cwahlmann/vz200/3d-model/aufkleber_tasten_einzeln/key_1.png

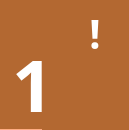
3d-model/aufkleber_tasten_einzeln/key_1.png
