cwahlmann/vz200/3d-model/aufkleber_tasten_einzeln/key_5.png

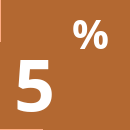
3d-model/aufkleber_tasten_einzeln/key_5.png
