cwahlmann/vz200/3d-model/aufkleber_tasten_einzeln/key_8.png

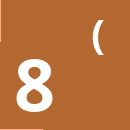
3d-model/aufkleber_tasten_einzeln/key_8.png
