cwahlmann/vz200/3d-model/aufkleber_tasten_einzeln/key_I.png

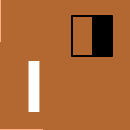
3d-model/aufkleber_tasten_einzeln/key_I.png
