cwahlmann/vz200/3d-model/aufkleber_tasten_einzeln/key_M.png

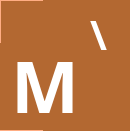
3d-model/aufkleber_tasten_einzeln/key_M.png
