cwahlmann/vz200/3d-model/aufkleber_tasten_einzeln/key_minus.png

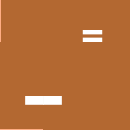
3d-model/aufkleber_tasten_einzeln/key_minus.png
