cwahlmann/vz200/3d-model/aufkleber_tasten_einzeln/key_N.png

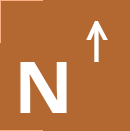
3d-model/aufkleber_tasten_einzeln/key_N.png
