cwahlmann/vz200/3d-model/aufkleber_tasten_einzeln/key_Q.png

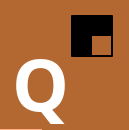
3d-model/aufkleber_tasten_einzeln/key_Q.png
