cwahlmann/vz200/3d-model/Lüftungsgitter.png

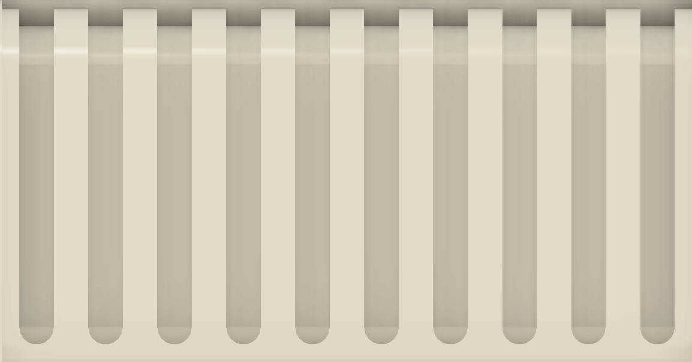
3d-model/Lüftungsgitter.png
