cwahlmann/vz200/3d-model/Lüftungsgitter_transparent.png

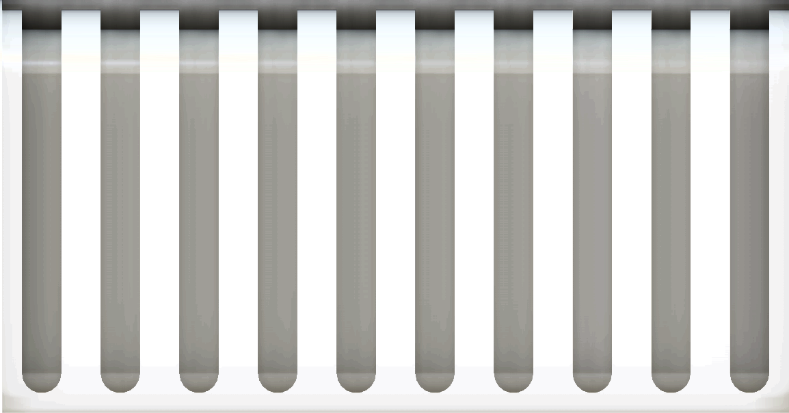
3d-model/Lüftungsgitter_transparent.png
