cwahlmann/vz200/3d-model/Rückseite Aufkleber.png

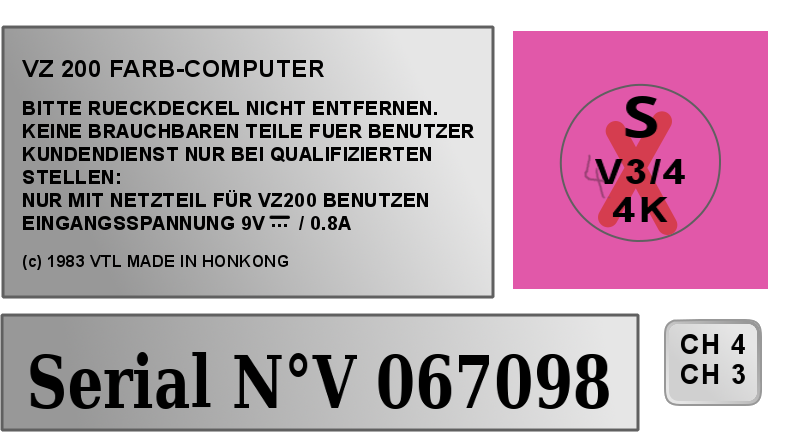
3d-model/Rückseite Aufkleber.png
