cwahlmann/vz200/3d-model/Tastatur_Aufkleber.png

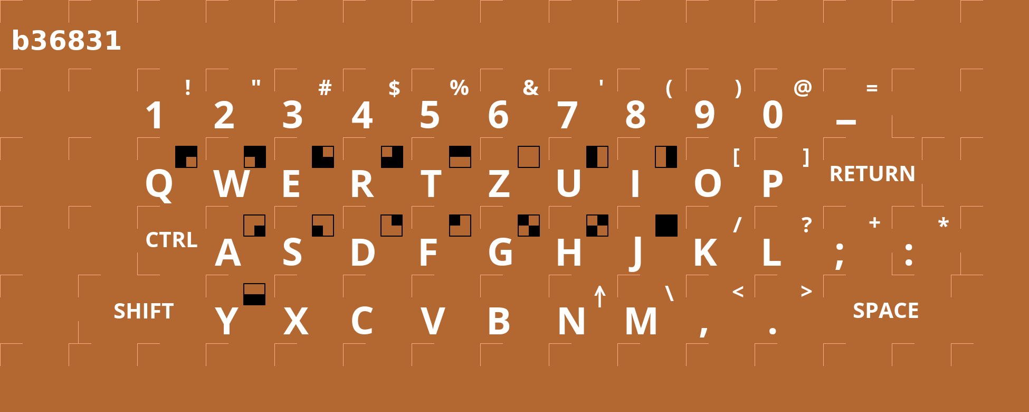
3d-model/Tastatur_Aufkleber.png
