cwahlmann/vz200/3d-model/Tastatur_Aufkleber_7x_70perc_A4.png

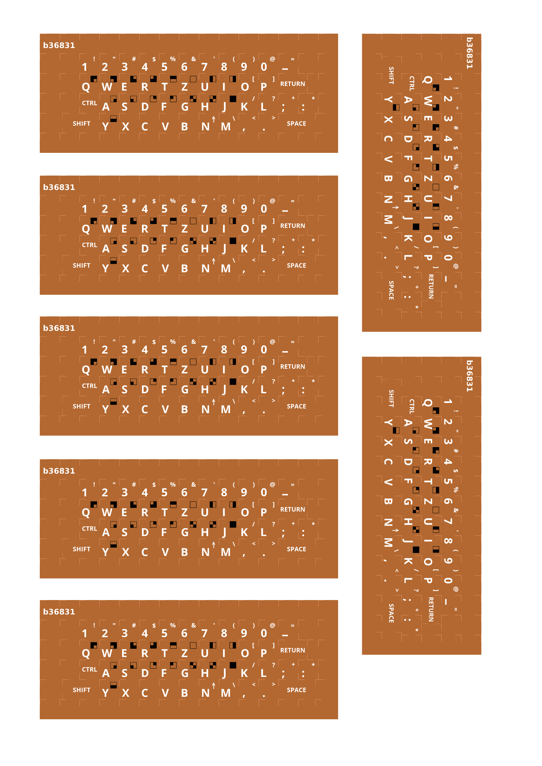
3d-model/Tastatur_Aufkleber_7x_70perc_A4.png
