cwahlmann/vz200/3d-model/Tastatur_mini_A4.png

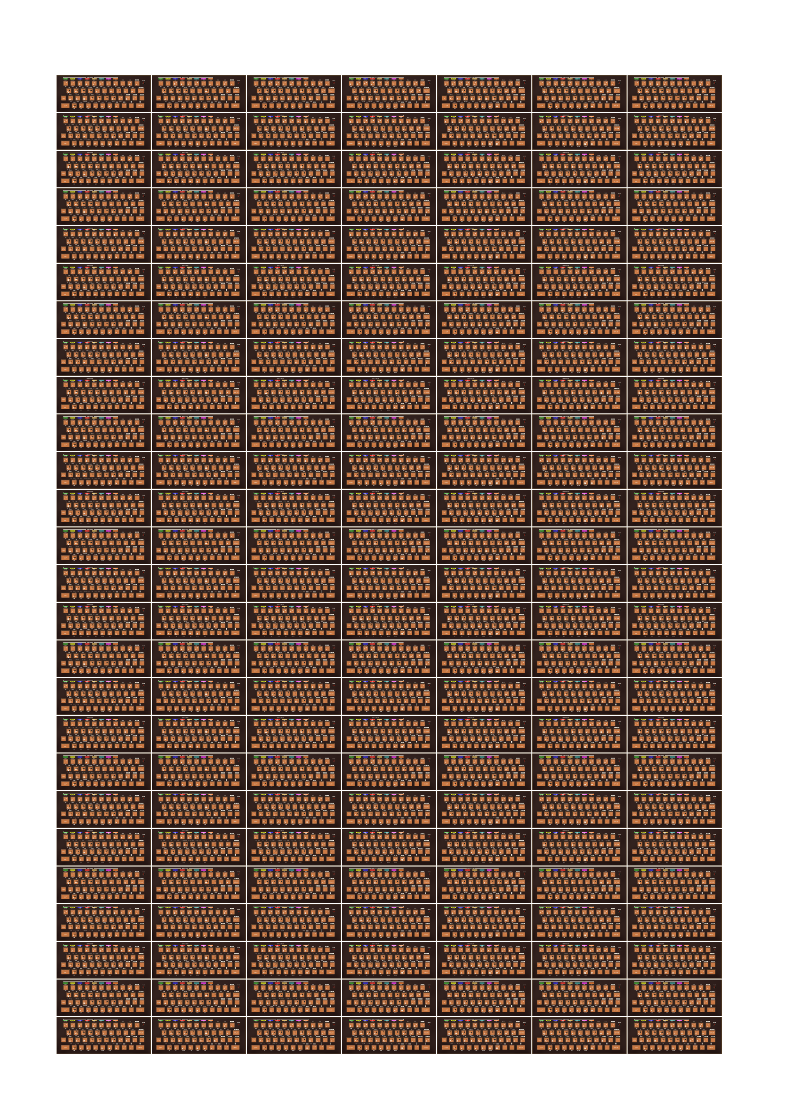
3d-model/Tastatur_mini_A4.png
