cwahlmann/vz200/3d-model/tastaturschabloben_3x70_1x50_A4.png

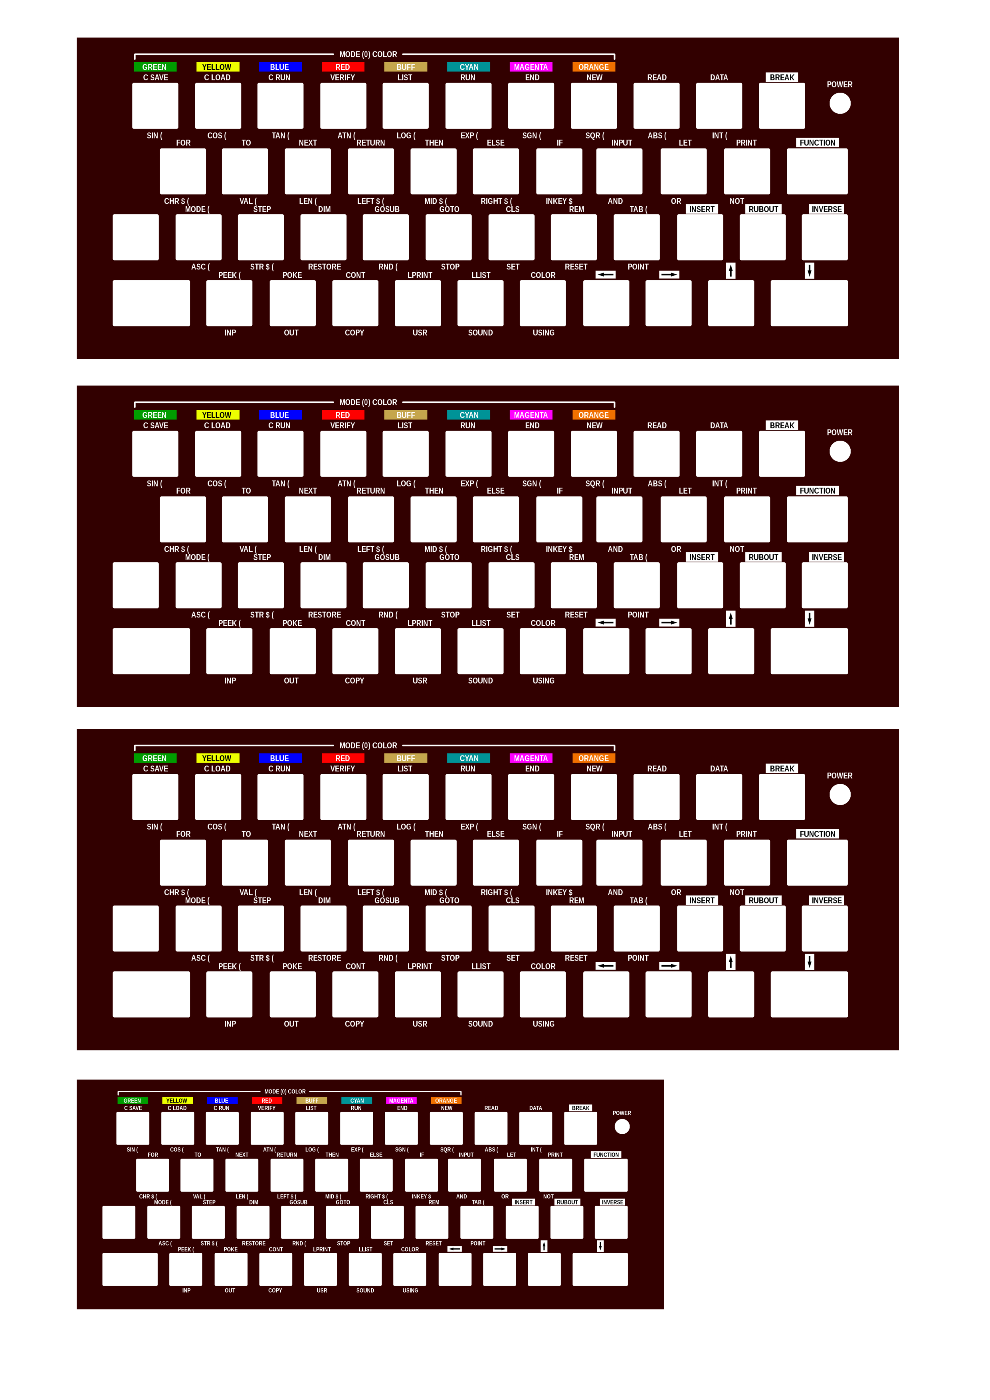
3d-model/tastaturschabloben_3x70_1x50_A4.png
