cwahlmann/vz200/3d-model/Tastaturschablone.png

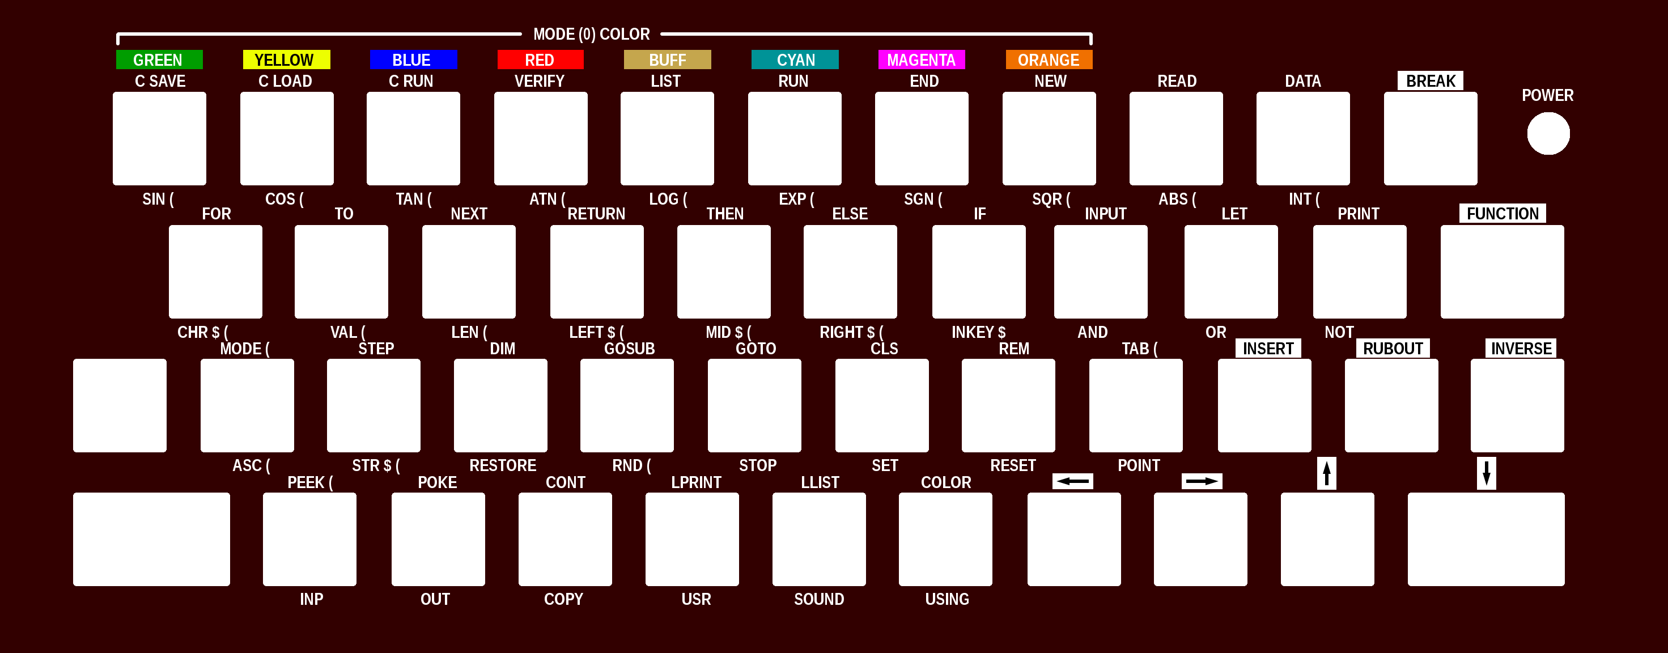
3d-model/Tastaturschablone.png
