cwahlmann/vz200/3d-model/VZ200-background.png

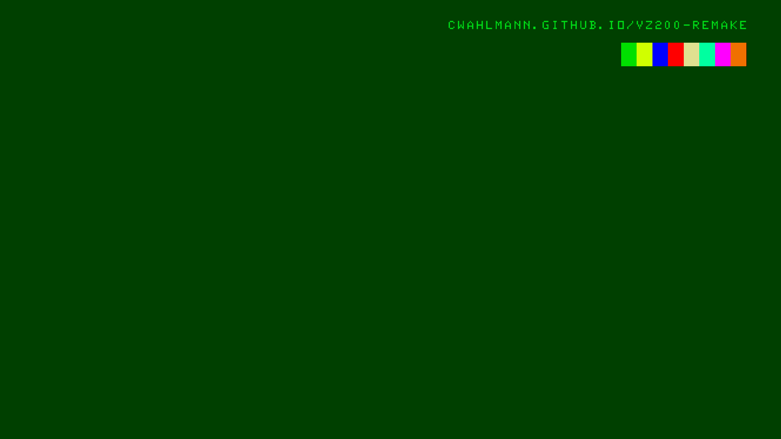
3d-model/VZ200-background.png
