cwahlmann/vz200/3d-model/vz200.png

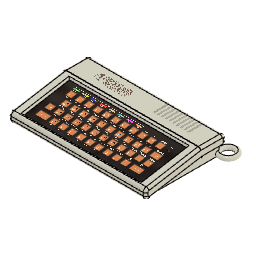
3d-model/vz200.png
