cwahlmann/vz200/emulator/desktop-wallpaper-2.png

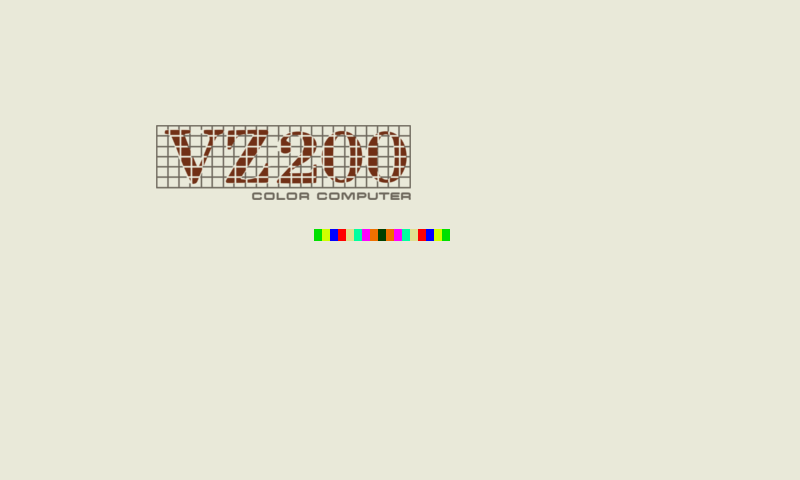
emulator/desktop-wallpaper-2.png
