cwahlmann/vz200/emulator/desktop-wallpaper-3.png

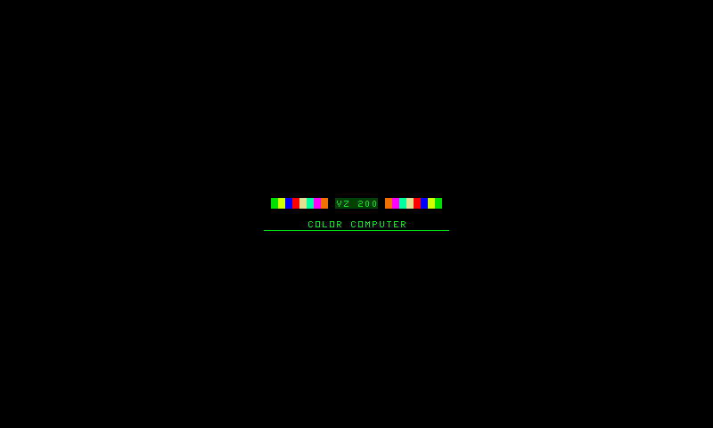
emulator/desktop-wallpaper-3.png
