cwahlmann/vz200/emulator/Tastatur.png

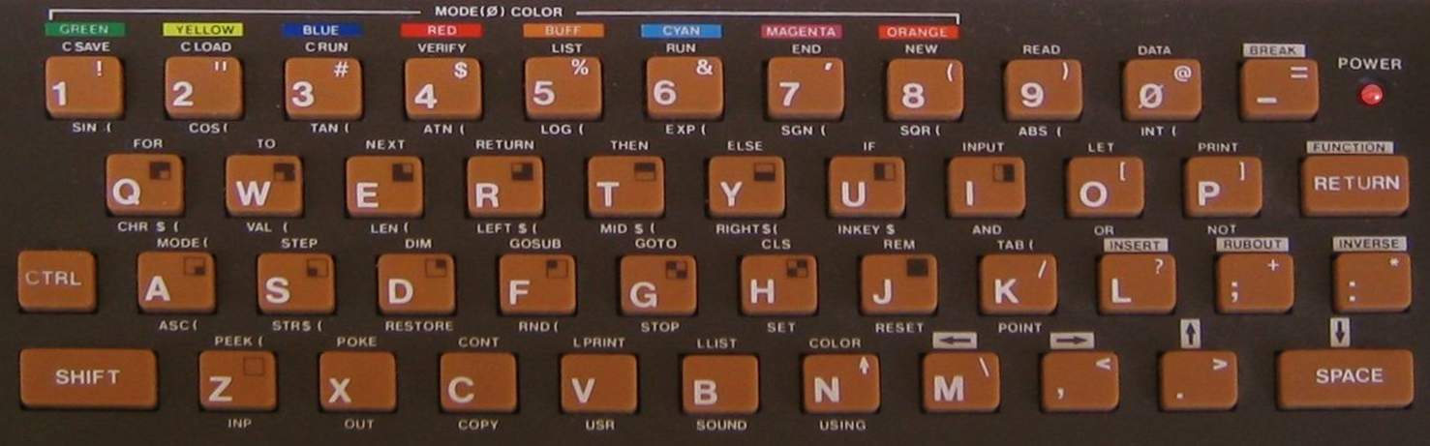
emulator/Tastatur.png
