cwahlmann/vz200/monitor/ASIS-Vintage-1983-RCA-CRT-13-Color-TV-_57 (2).jpg

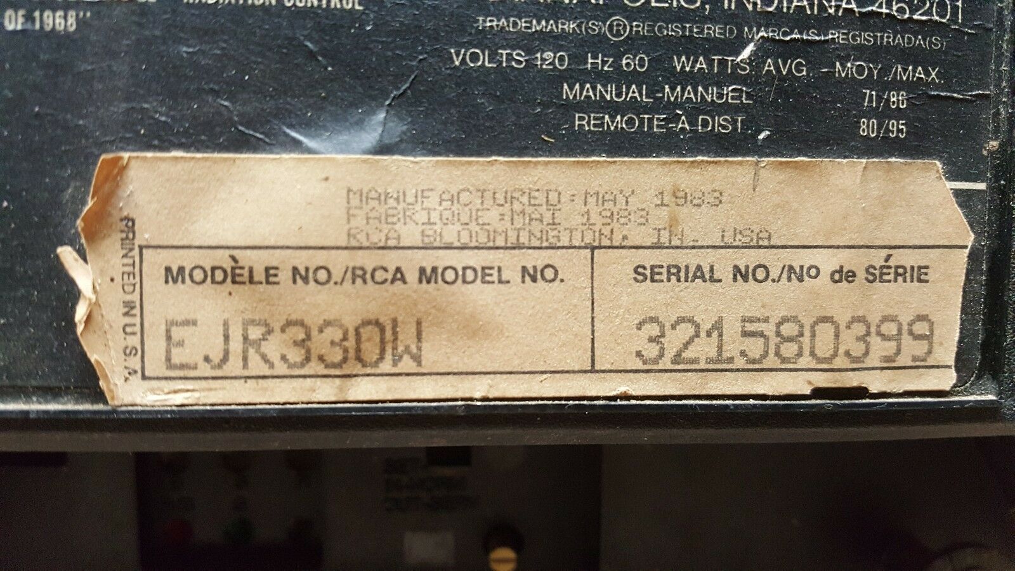
monitor/ASIS-Vintage-1983-RCA-CRT-13-Color-TV-_57 (2).jpg
