cwahlmann/vz200/screenshots/20190511_203651.jpg

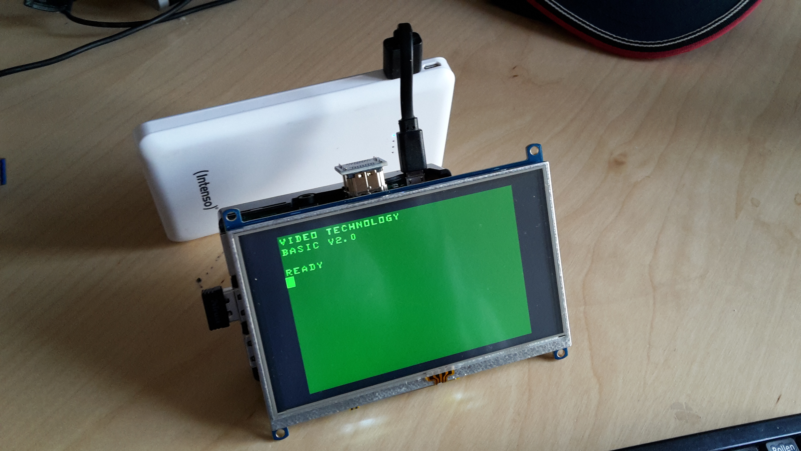
screenshots/20190511_203651.jpg
