cwahlmann/vz200/screenshots/20190511_203712.jpg

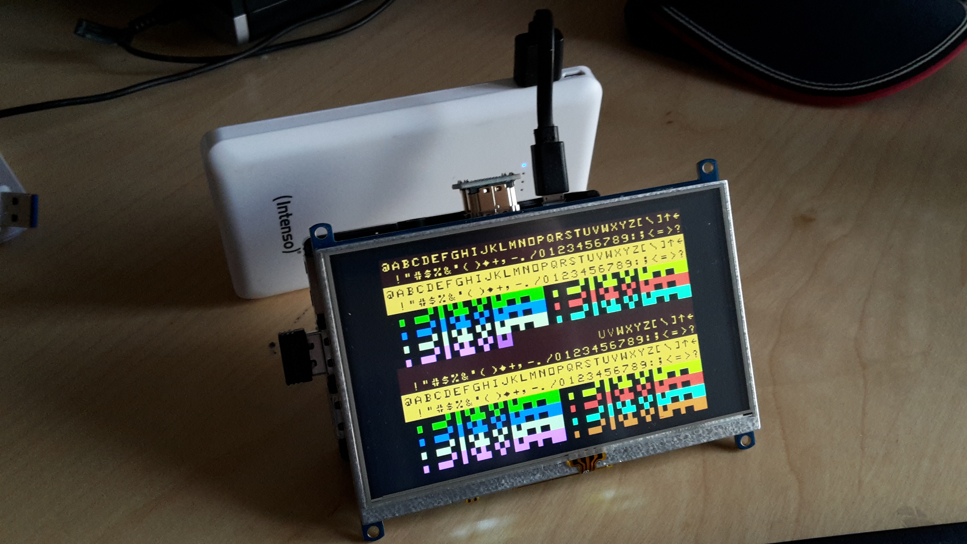
screenshots/20190511_203712.jpg
