cwahlmann/vz200/screenshots/20190511_203717.jpg

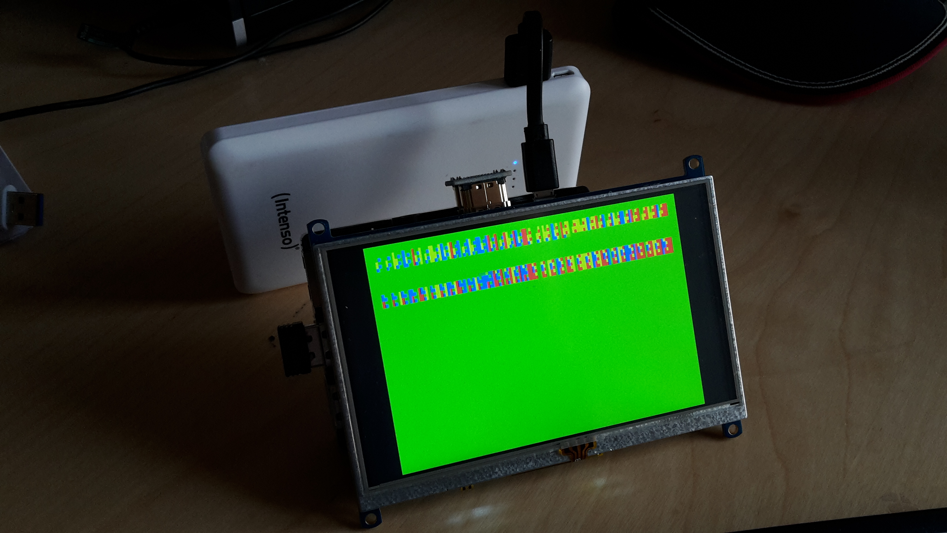
screenshots/20190511_203717.jpg
