cwahlmann/vz200/screenshots/20190511_203816.jpg

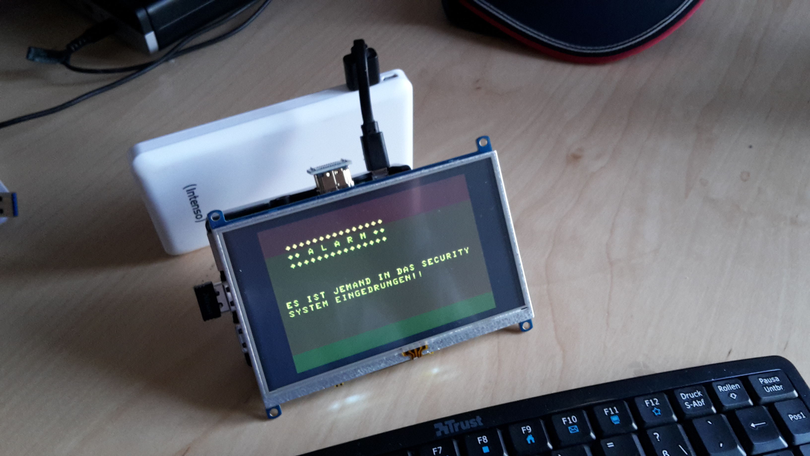
screenshots/20190511_203816.jpg
