cwahlmann/vz200/screenshots/halloWeltAsm.jpg

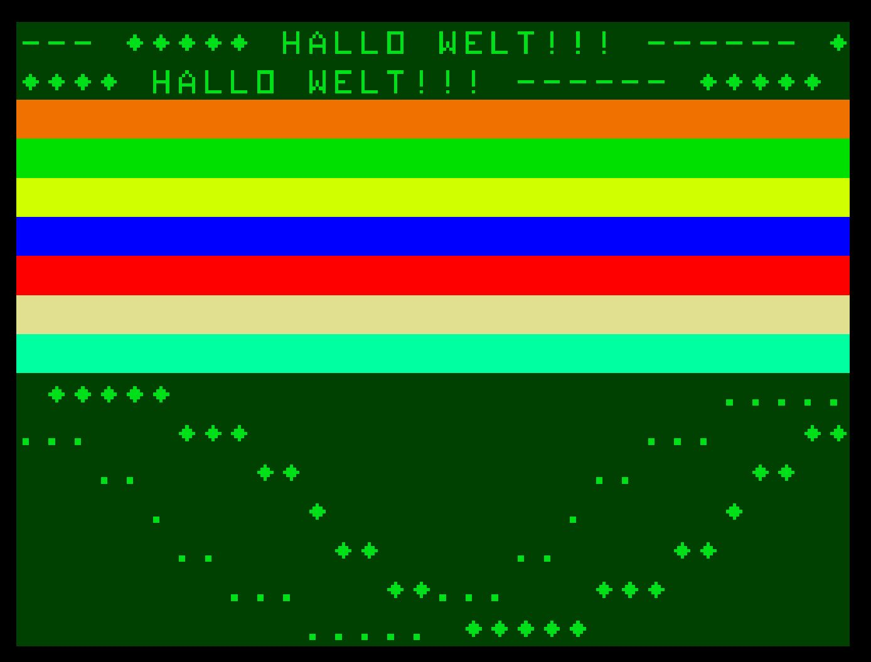
screenshots/halloWeltAsm.jpg
