cwahlmann/vz200/screenshots/Prototyp-02.jpg

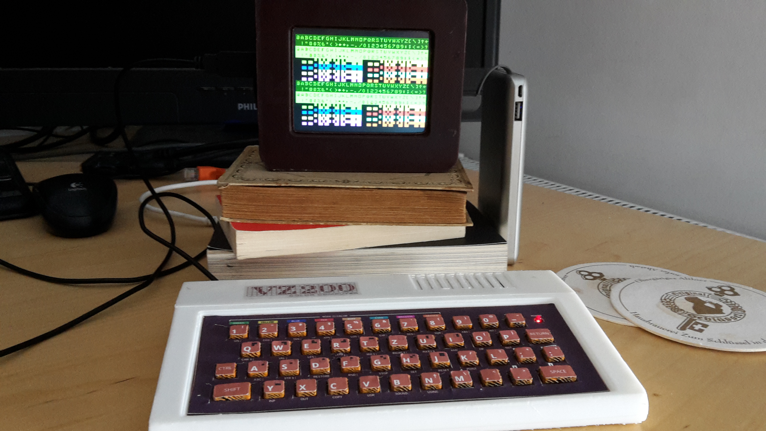
screenshots/Prototyp-02.jpg
