cwahlmann/vz200/screenshots/Prototyp-03.jpg

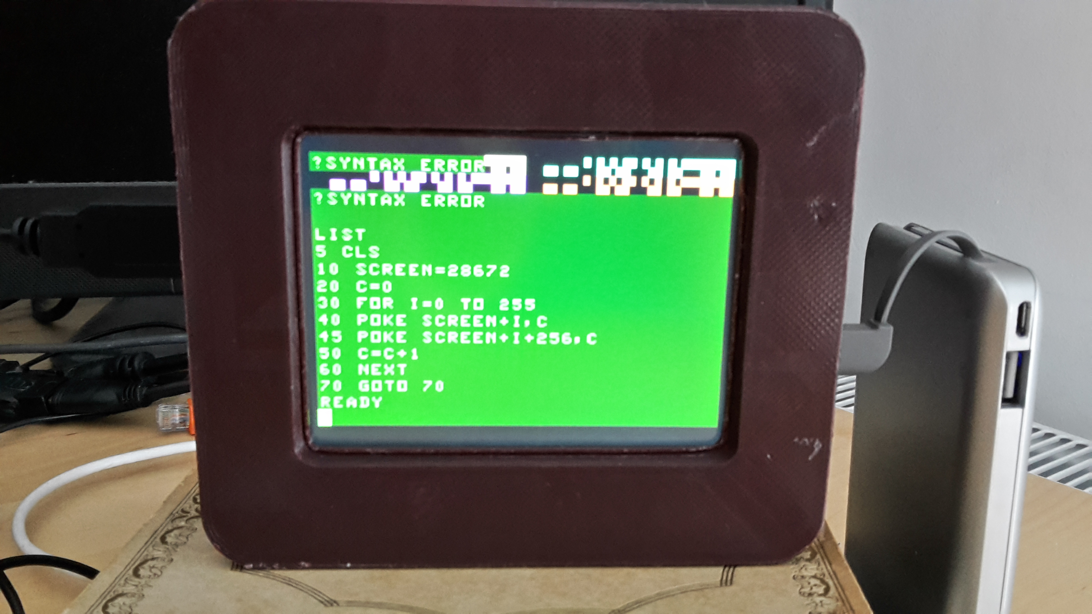
screenshots/Prototyp-03.jpg
