cwahlmann/vz200/screenshots/Prototyp-04.jpg

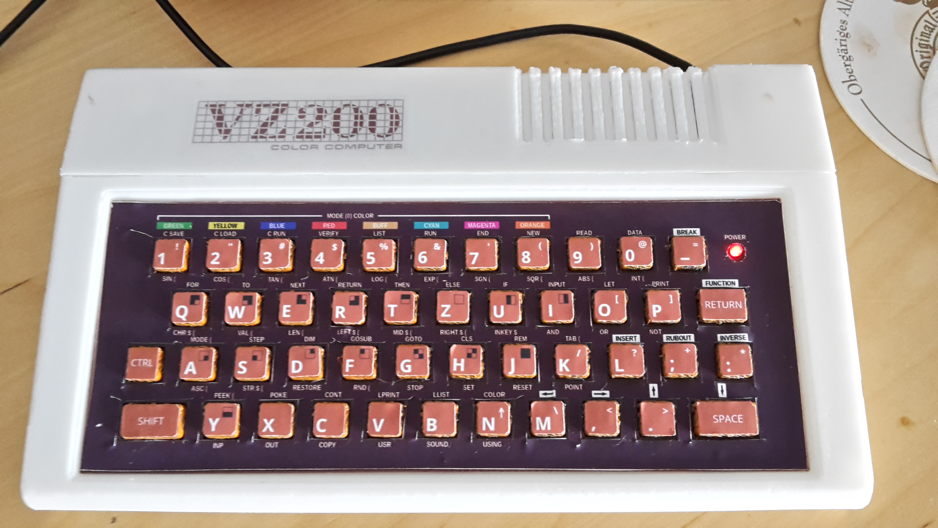
screenshots/Prototyp-04.jpg
