cwahlmann/vz200/screenshots/Prototyp-05.jpg

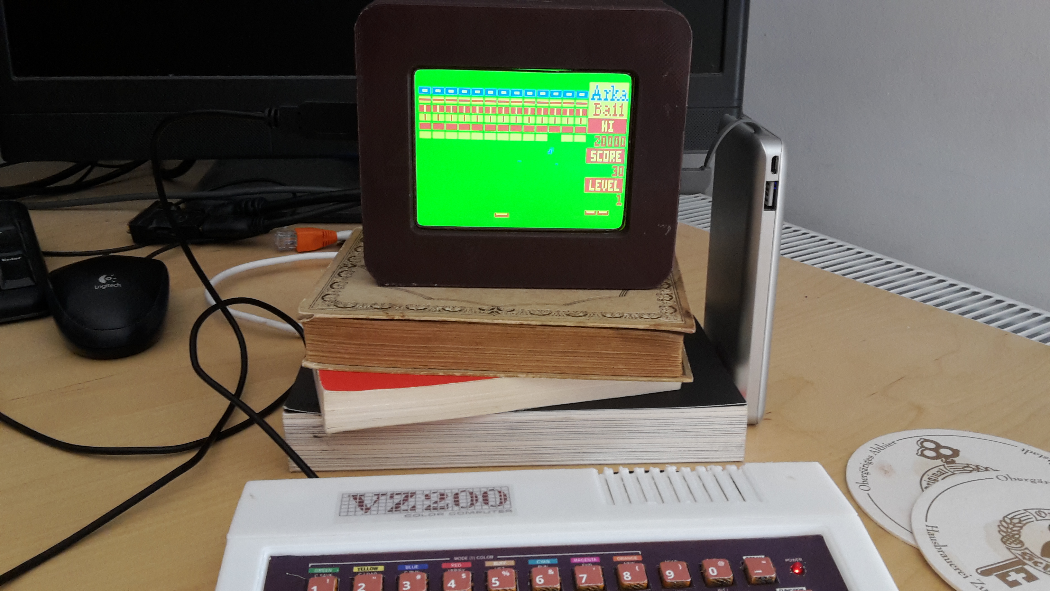
screenshots/Prototyp-05.jpg
