cwahlmann/vz200/screenshots/Prototyp_01.jpg

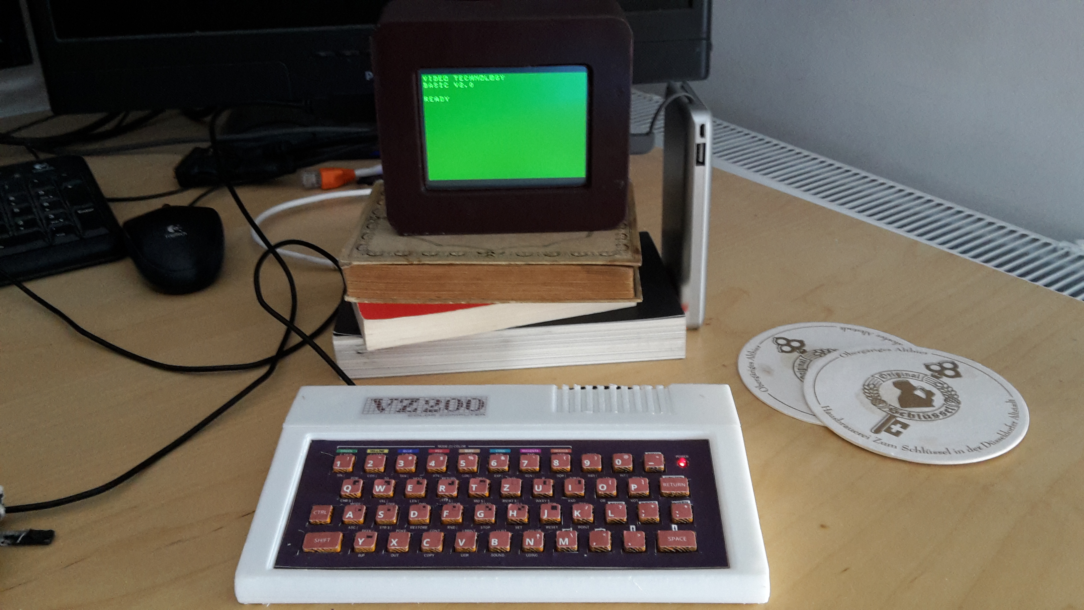
screenshots/Prototyp_01.jpg
