cwahlmann/vz200/screenshots/tastatur_orange_lack_50perc_1.jpg

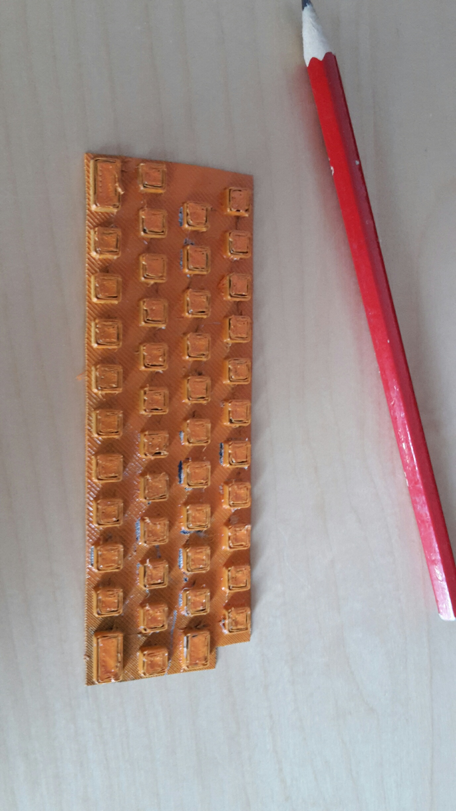
screenshots/tastatur_orange_lack_50perc_1.jpg
