cwahlmann/vz200/screenshots/tastatur_orange_lack_70perc_1.jpg

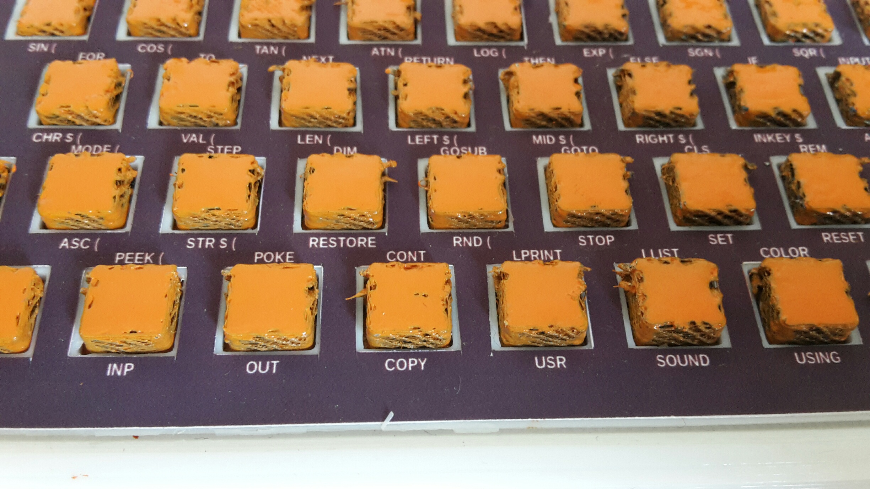
screenshots/tastatur_orange_lack_70perc_1.jpg
