cwahlmann/vz200/screenshots/tastatur_orange_lack_70perc_2.jpg

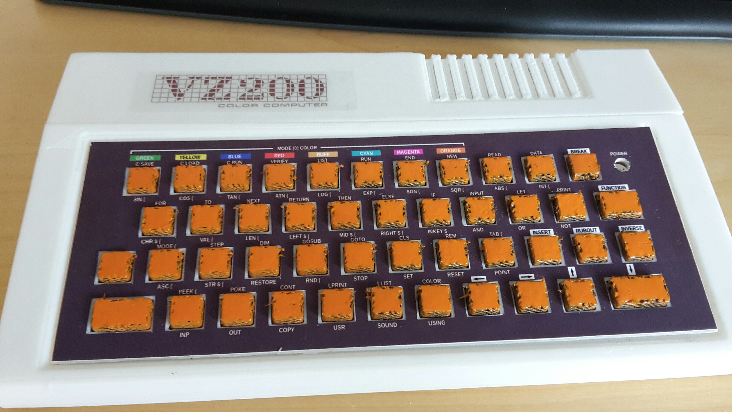
screenshots/tastatur_orange_lack_70perc_2.jpg
