cwahlmann/vz200/screenshots/tastaturfolie_angepasst_1.jpg

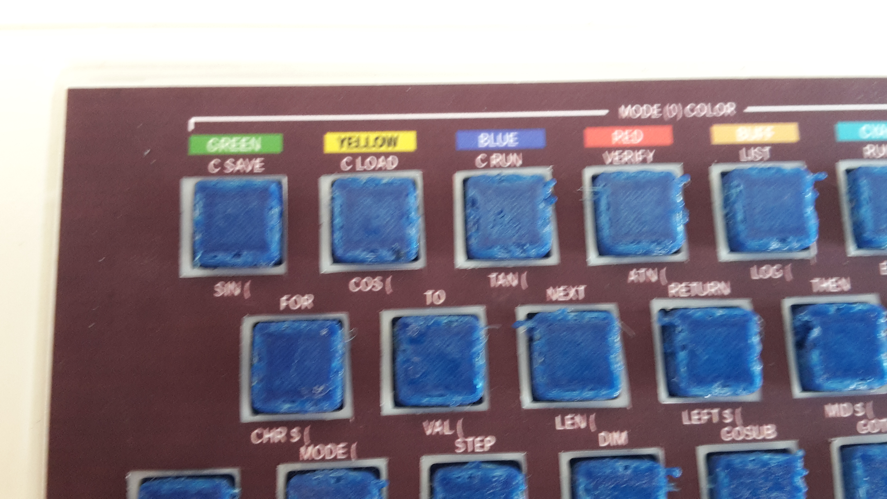
screenshots/tastaturfolie_angepasst_1.jpg
