cwahlmann/vz200/screenshots/tastaturfolie_angepasst_2.jpg

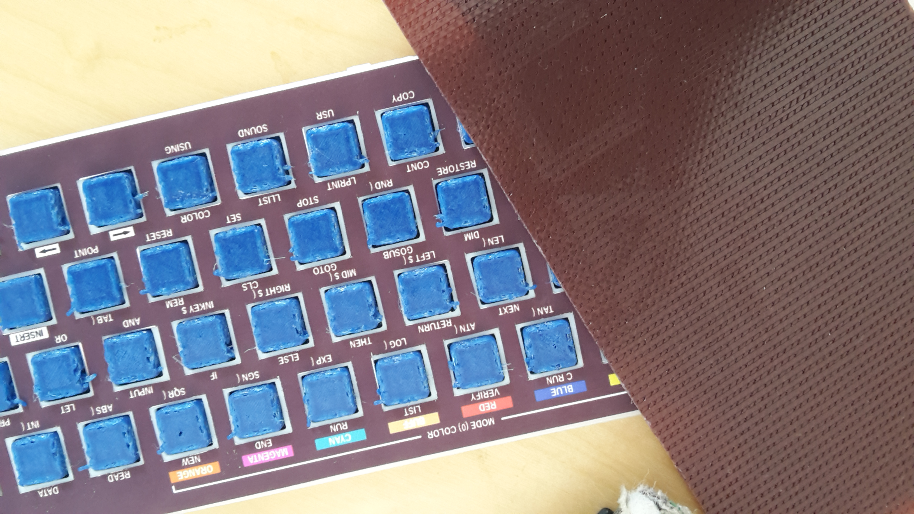
screenshots/tastaturfolie_angepasst_2.jpg
