cwahlmann/vz200/screenshots/tastaturfolie_angepasst_3.jpg

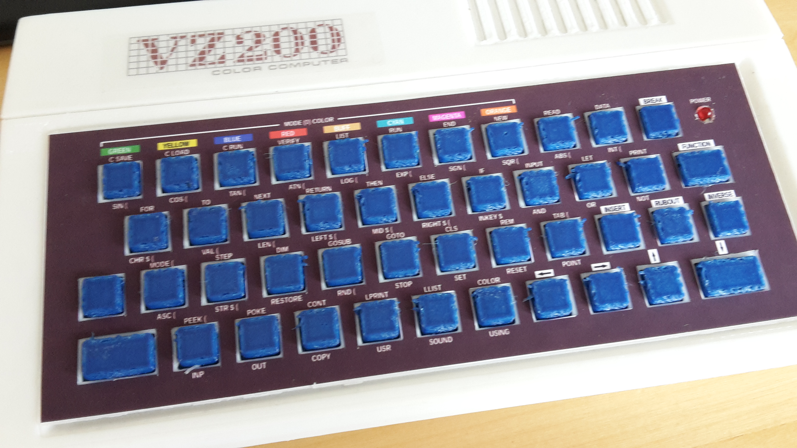
screenshots/tastaturfolie_angepasst_3.jpg
