cwahlmann/vz200/3d-model/drucke/stl/VZ200_Gehäuse unten_rechteSeite_test_70%.stl

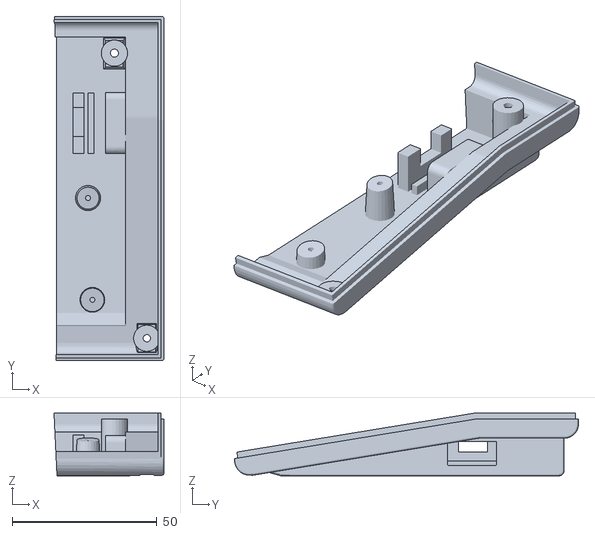
[picture p95: CAD file, 2019-08-07]
3d-model/drucke/stl/VZ200_Gehäuse unten_rechteSeite_test_70%.stl
38.1 x 119.0 x 21.7
