cwahlmann/vz200/3d-model/drucke/Cura/CE3_VZ200_Gehause oben_vorn_70Prozent.3mf

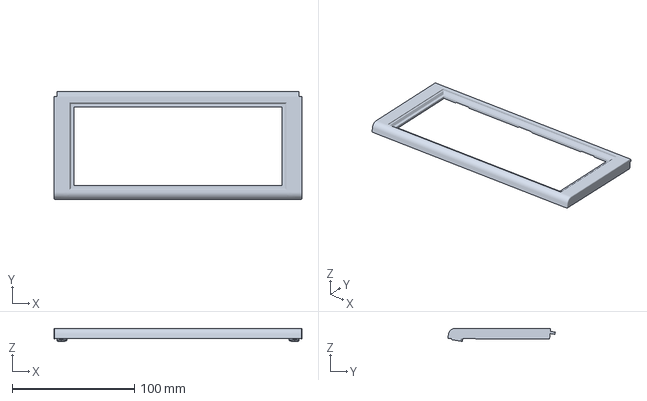
[picture p96: CAD file, 2019-11-27]
3d-model/drucke/Cura/CE3_VZ200_Gehause oben_vorn_70Prozent.3mf
203.0 x 88.1 x 10.7 mm
