cwahlmann/vz200/3d-model/drucke/stl/VZ200_Tastatur Rahmen_70%.stl

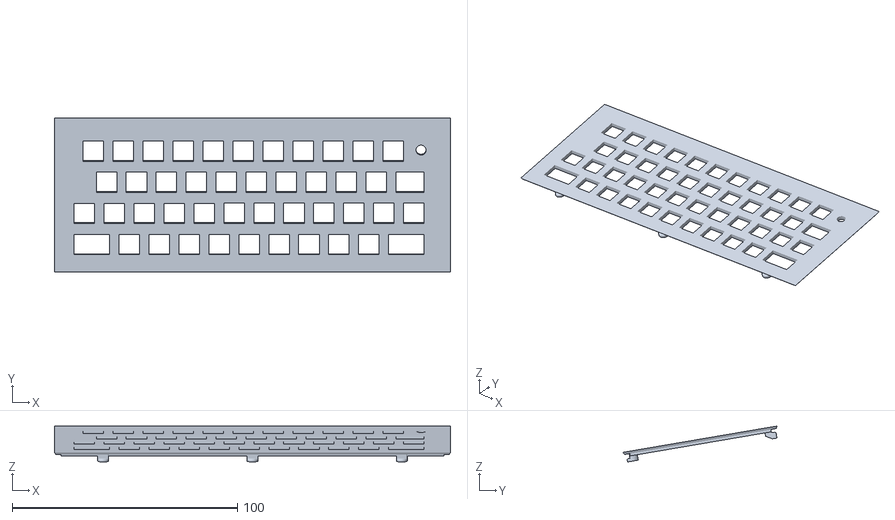
[picture p97: CAD file, 2019-08-07]
3d-model/drucke/stl/VZ200_Tastatur Rahmen_70%.stl
175.7 x 68.5 x 16.0
