cwahlmann/vz200/3d-model/drucke/stl/Monitor-Fuß-vorne.stl

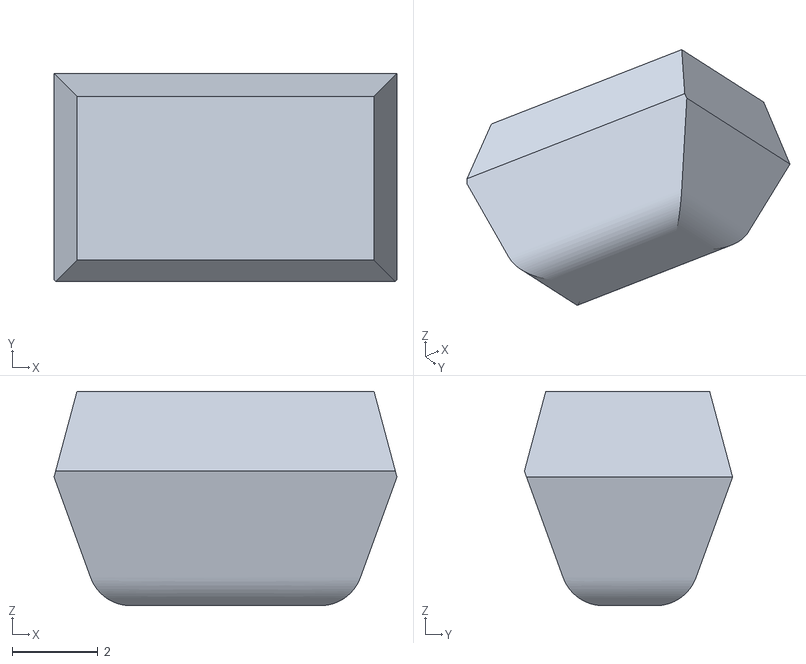
[picture p98: CAD file, 2019-08-07]
3d-model/drucke/stl/Monitor-Fuß-vorne.stl
8.00 x 4.86 x 5.00
