cwahlmann/vz200/3d-model/drucke/Cura/CE3_VZ200_Gehause unten_70%.3mf

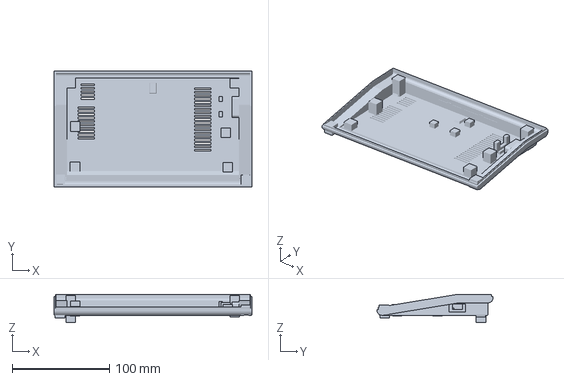
[picture p99: CAD file, 2019-09-23]
3d-model/drucke/Cura/CE3_VZ200_Gehause unten_70%.3mf
203.1 x 119.1 x 29.1 mm
