cwahlmann/vz200/3d-model/drucke/stl/VZ200_Resetschalter-Klemme70%.stl

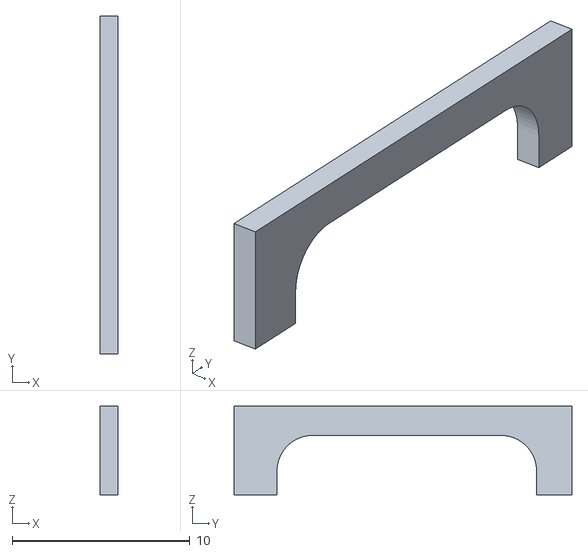
[picture p100: CAD file, 2019-08-07]
3d-model/drucke/stl/VZ200_Resetschalter-Klemme70%.stl
1.00 x 19.0 x 5.00
