cwahlmann/vz200/3d-model/drucke/Cura/CE3_Monitor-Gehause-vorn.3mf

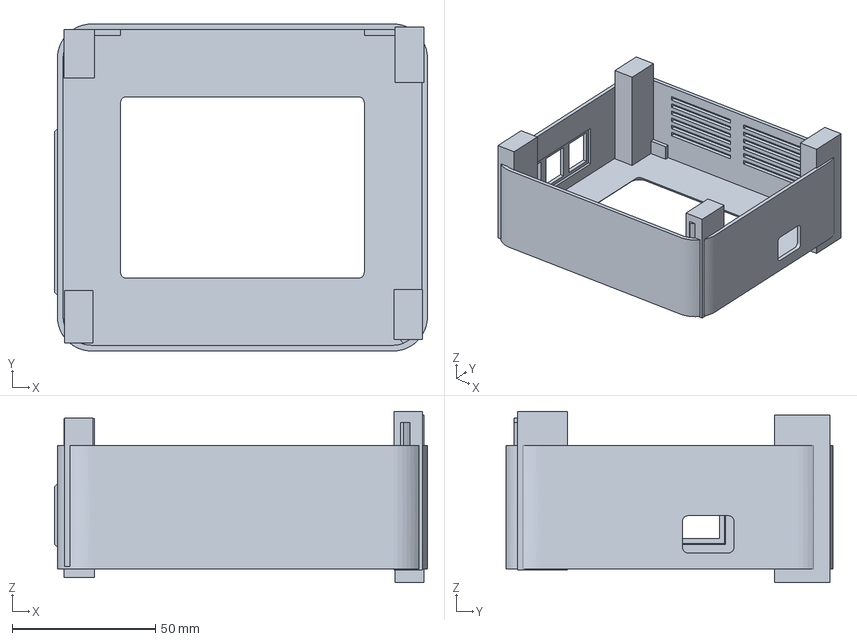
[picture p101: CAD file, 2019-09-08]
3d-model/drucke/Cura/CE3_Monitor-Gehause-vorn.3mf
130.0 x 114.0 x 59.7 mm
