cwahlmann/vz200/3d-model/drucke/stl/VZ200_Resetschalter70%.stl

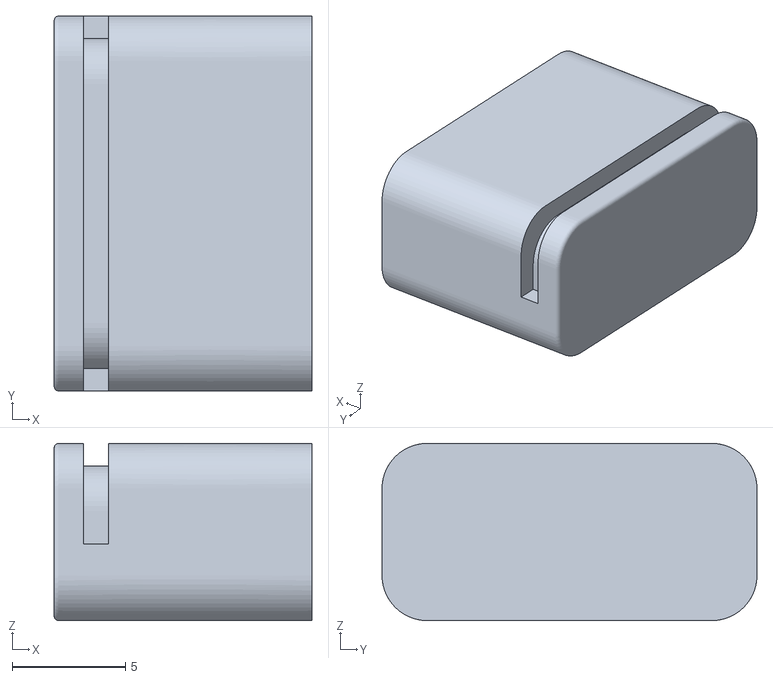
[picture p102: CAD file, 2019-08-07]
3d-model/drucke/stl/VZ200_Resetschalter70%.stl
11.4 x 16.6 x 7.84
