cwahlmann/vz200/3d-model/drucke/stl/Monitor-Gehäuse-hinten.stl

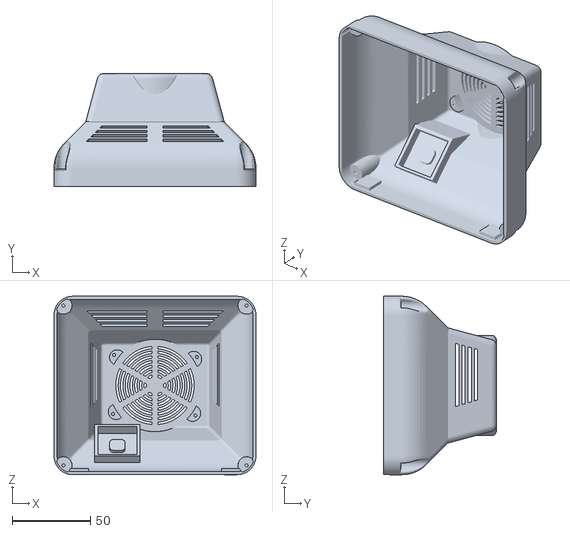
[picture p103: CAD file, 2019-08-01]
3d-model/drucke/stl/Monitor-Gehäuse-hinten.stl
129.0 x 72.0 x 114.1
