cwahlmann/vz200/3d-model/drucke/Cura/CE3_Monitor-Fuß-vorne.3mf

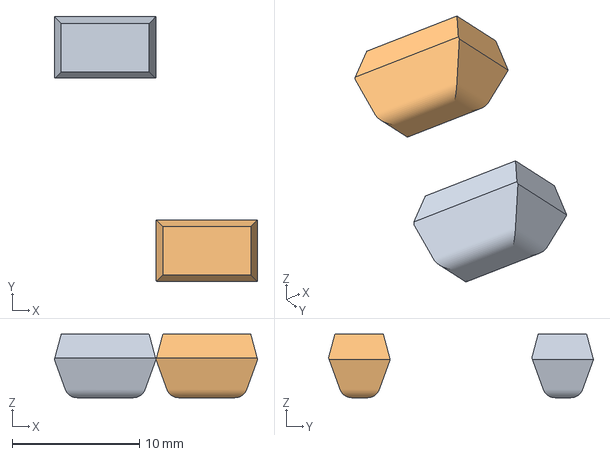
[picture p104: CAD file, 2019-08-07]
3d-model/drucke/Cura/CE3_Monitor-Fuß-vorne.3mf
16.0 x 20.9 x 5.00 mm
