cwahlmann/vz200/3d-model/drucke/stl/Applikationen-vorne.stl

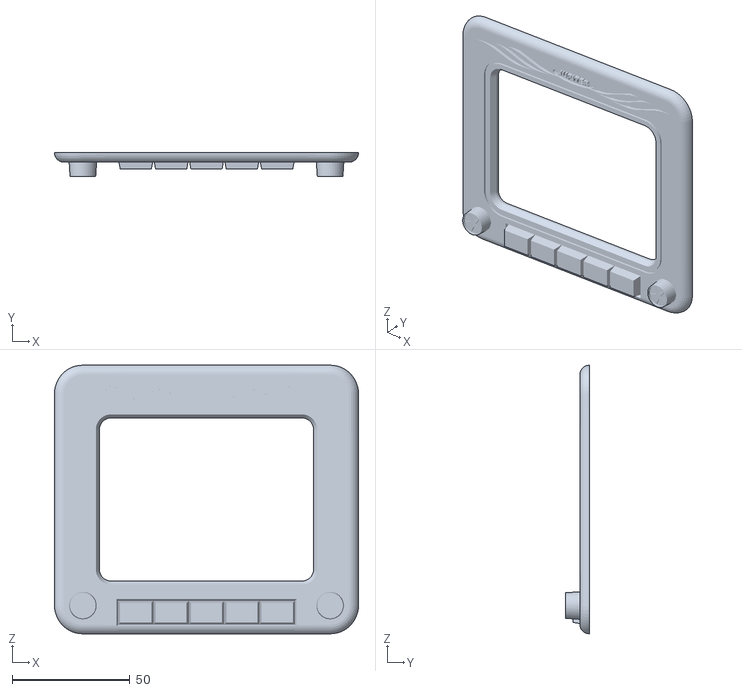
[picture p105: CAD file, 2019-08-01]
3d-model/drucke/stl/Applikationen-vorne.stl
129.0 x 10.0 x 114.0
