cwahlmann/vz200/3d-model/drucke/Cura/CE3_VZ200_Resetschalter-Klemme70%.3mf

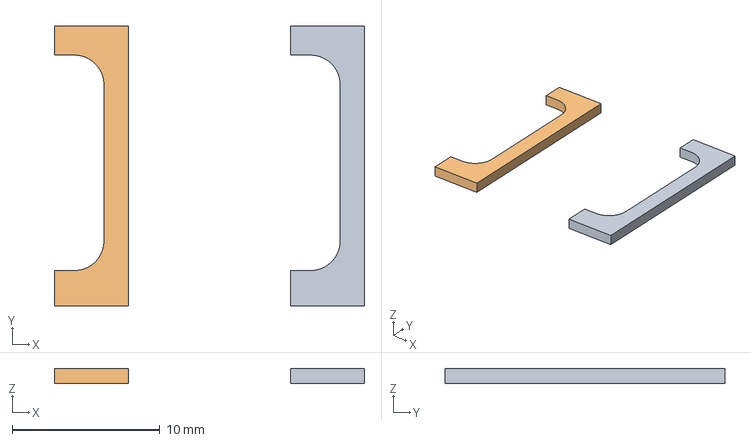
[picture p106: CAD file, 2019-08-07]
3d-model/drucke/Cura/CE3_VZ200_Resetschalter-Klemme70%.3mf
21.0 x 19.0 x 1.00 mm
