cwahlmann/vz200/3d-model/drucke/stl/Lautsprecher-Halterung.stl

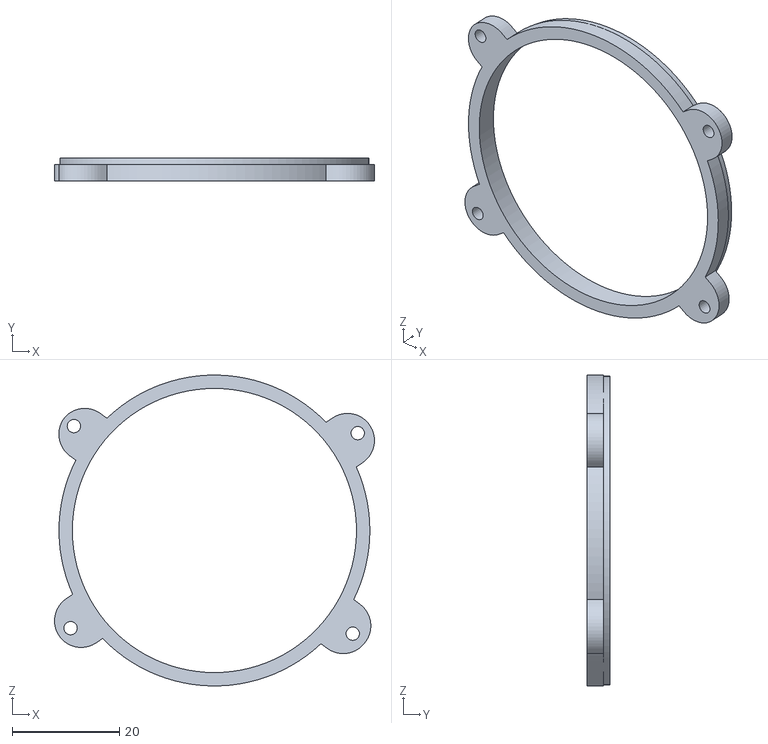
[picture p107: CAD file, 2019-08-01]
3d-model/drucke/stl/Lautsprecher-Halterung.stl
59.7 x 4.22 x 58.0
