cwahlmann/vz200/3d-model/drucke/Cura/CE3_VZ200-Schild.3mf

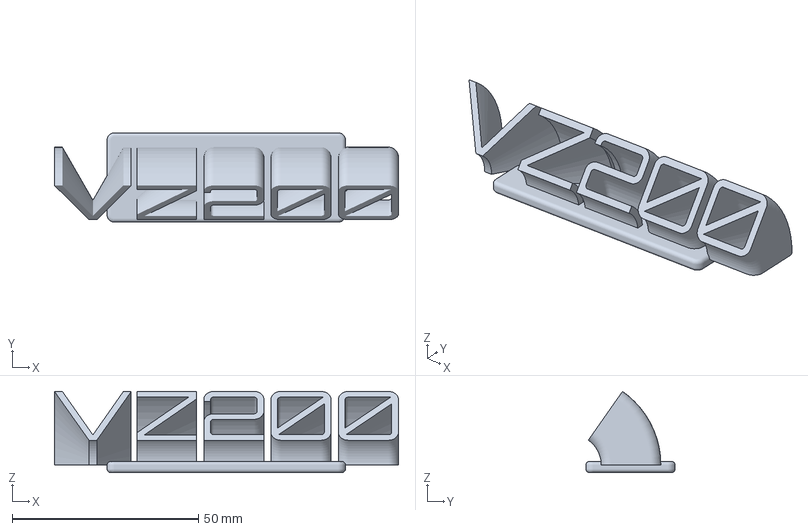
[picture p108: CAD file, 2019-08-01]
3d-model/drucke/Cura/CE3_VZ200-Schild.3mf
92.3 x 24.0 x 21.8 mm
