cwahlmann/vz200/3d-model/drucke/stl/Monitor-Gehäuse-vorn.stl

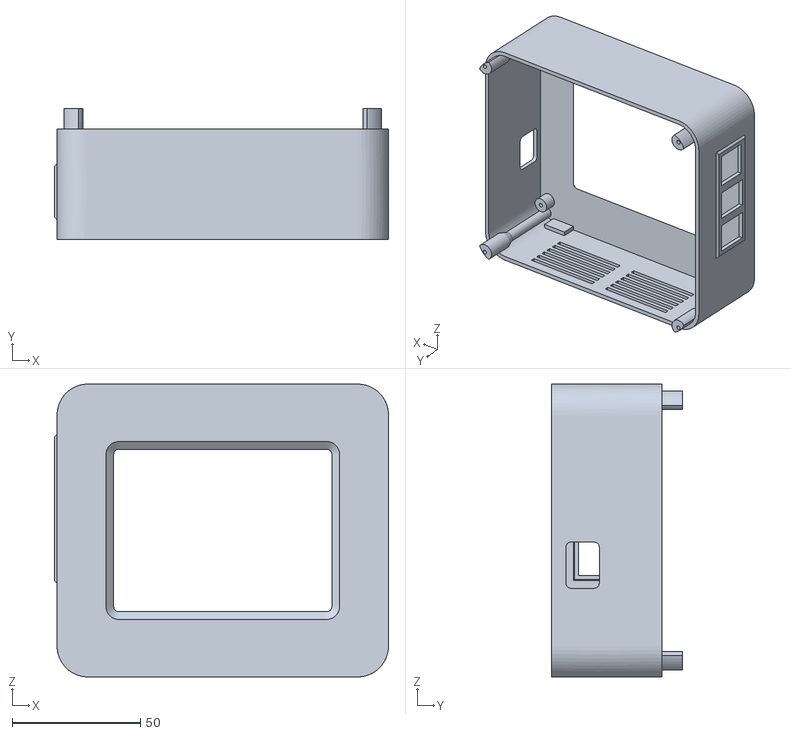
[picture p109: CAD file, 2019-07-11]
3d-model/drucke/stl/Monitor-Gehäuse-vorn.stl
130.0 x 51.0 x 114.0
