cwahlmann/vz200/3d-model/drucke/stl/Fuß.stl

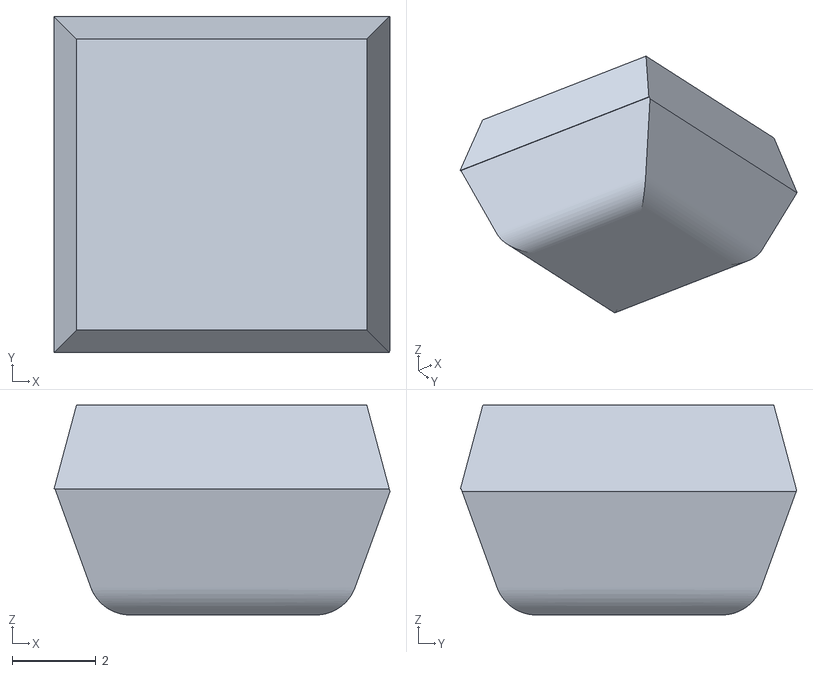
[picture p110: CAD file, 2019-06-30]
3d-model/drucke/stl/Fuß.stl
8.00 x 8.01 x 5.00
