cwahlmann/vz200/3d-model/drucke/stl/VZ200_Tastatur Tasten_5.5_70%.stl

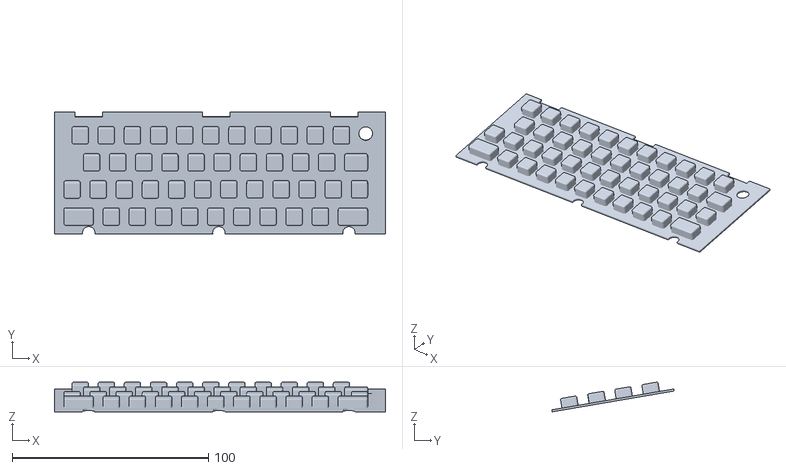
[picture p111: CAD file, 2019-06-30]
3d-model/drucke/stl/VZ200_Tastatur Tasten_5.5_70%.stl
168.5 x 62.3 x 15.1
