cwahlmann/vz200/3d-model/drucke/Cura/CE3_Lautsprecher-Halterung.3mf

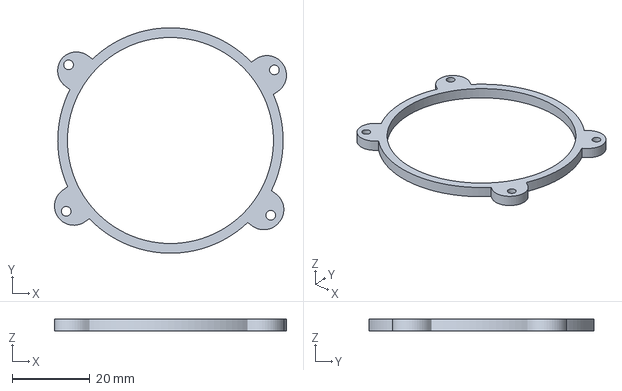
[picture p112: CAD file, 2019-08-01]
3d-model/drucke/Cura/CE3_Lautsprecher-Halterung.3mf
59.7 x 58.0 x 3.00 mm
