cwahlmann/vz200/3d-model/drucke/stl/VZ200_Schalter70%.stl

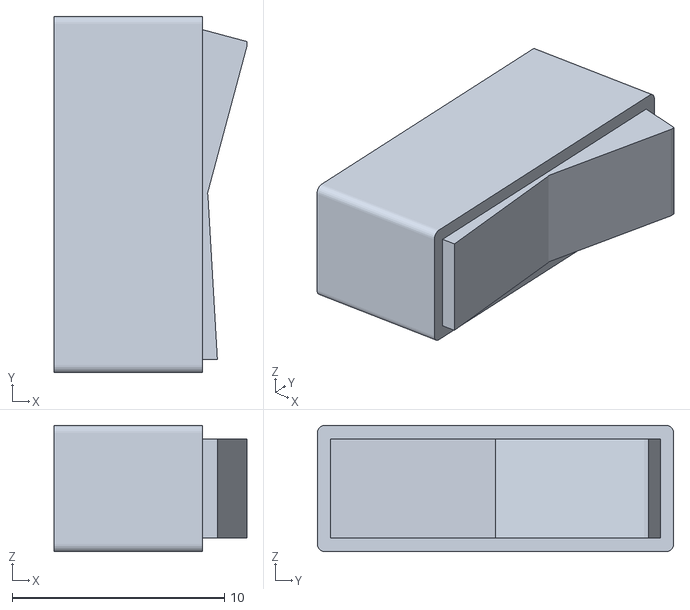
[picture p113: CAD file, 2019-06-19]
3d-model/drucke/stl/VZ200_Schalter70%.stl
9.10 x 16.8 x 5.95
