cwahlmann/vz200/3d-model/drucke/Cura/CE3_Fuß.3mf

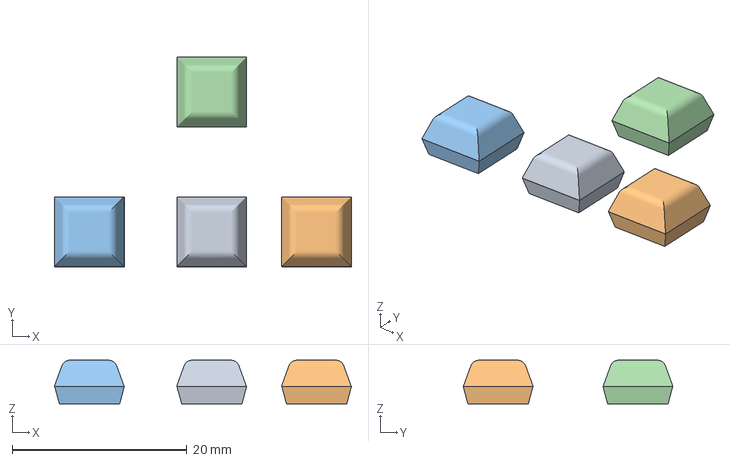
[picture p114: CAD file, 2019-06-30]
3d-model/drucke/Cura/CE3_Fuß.3mf
34.0 x 24.0 x 5.00 mm
