cwahlmann/vz200/3d-model/drucke/Cura/CE3_VZ200_Tastatur Tasten_5.5_35%_DualFilament_TPU_WOOD.3mf

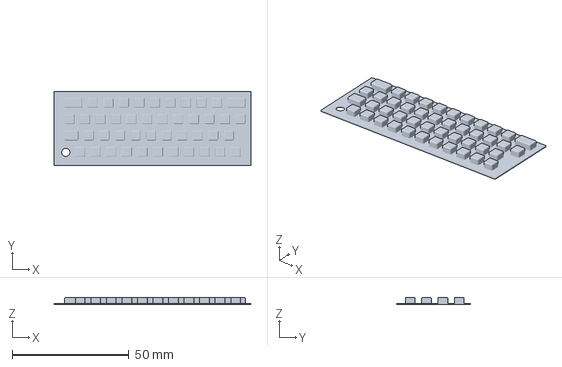
[picture p115: CAD file, 2019-06-30]
3d-model/drucke/Cura/CE3_VZ200_Tastatur Tasten_5.5_35%_DualFilament_TPU_WOOD.3mf
84.2 x 31.5 x 2.98 mm
