cwahlmann/vz200/3d-model/drucke/Cura/CE3_Monitor_VorderseiteMitFüßen_PLA_White.3mf

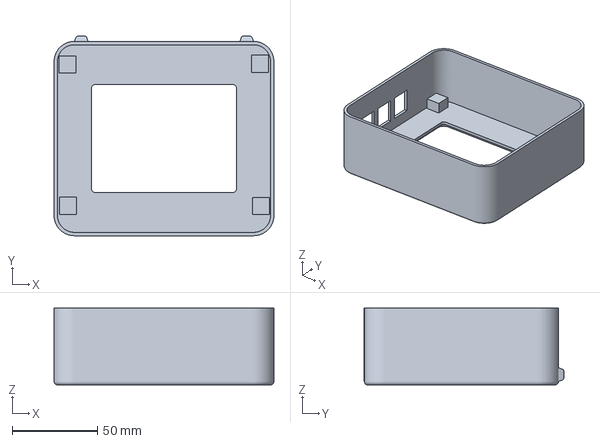
[picture p116: CAD file, 2019-06-30]
3d-model/drucke/Cura/CE3_Monitor_VorderseiteMitFüßen_PLA_White.3mf
129.0 x 117.0 x 45.0 mm
