cwahlmann/vz200/3d-model/drucke/Cura/CE3_VZ200_Leisten unten 70%.3mf

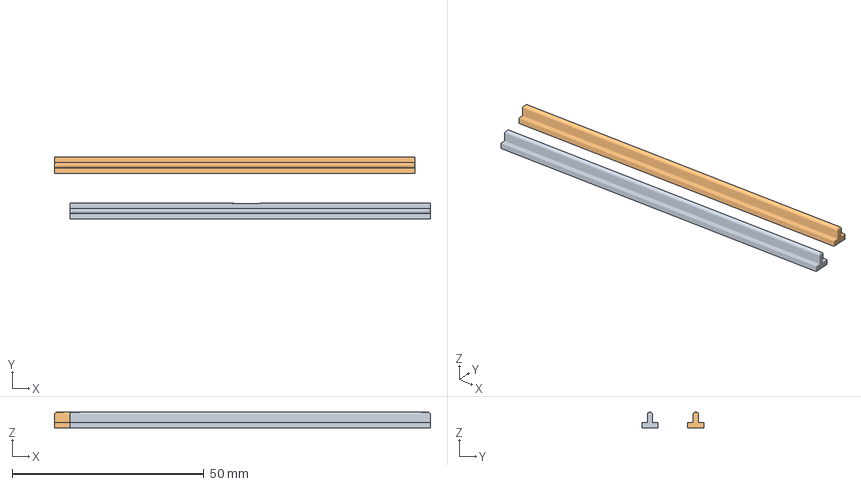
[picture p117: CAD file, 2019-06-19]
3d-model/drucke/Cura/CE3_VZ200_Leisten unten 70%.3mf
98.1 x 16.2 x 4.16 mm
