cwahlmann/vz200/3d-model/drucke/Cura/CE3_VZ200_Steg_Füße_70%.3mf

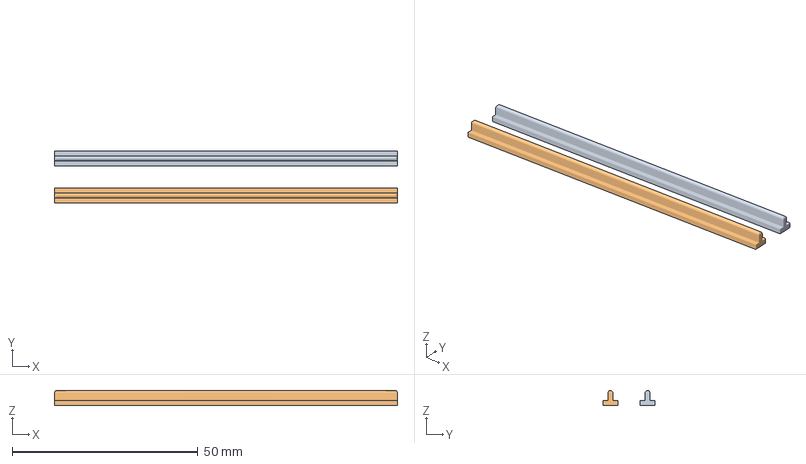
[picture p118: CAD file, 2019-06-09]
3d-model/drucke/Cura/CE3_VZ200_Steg_Füße_70%.3mf
92.3 x 14.0 x 4.08 mm
